ET-GH/AMBAR/AMBAR Ground Station mac build/GroundStation_autogen/EWIEGA46WW/moc_flightgraphcontroller.cpp

/****************************************************************************
** Meta object code from reading C++ file 'flightgraphcontroller.h'
**
** Created by: The Qt Meta Object Compiler version 69 (Qt 6.11.1)
**
** WARNING! All changes made in this file will be lost!
*****************************************************************************/

#include "../../../../flightgraphcontroller.h"
#include <QtCore/qmetatype.h>

#include <QtCore/qtmochelpers.h>

#include <memory>


#include <QtCore/qxptype_traits.h>
#if !defined(Q_MOC_OUTPUT_REVISION)
#error "The header file 'flightgraphcontroller.h' doesn't include <QObject>."
#elif Q_MOC_OUTPUT_REVISION != 69
#error "This file was generated using the moc from 6.11.1. It"
#error "cannot be used with the include files from this version of Qt."
#error "(The moc has changed too much.)"
#endif

#ifndef Q_CONSTINIT
#define Q_CONSTINIT
#endif

QT_WARNING_PUSH
QT_WARNING_DISABLE_DEPRECATED
QT_WARNING_DISABLE_GCC("-Wuseless-cast")
namespace {
struct qt_meta_tag_ZN21FlightGraphControllerE_t {};
} // unnamed namespace

template <> constexpr inline auto FlightGraphController::qt_create_metaobjectdata<qt_meta_tag_ZN21FlightGraphControllerE_t>()
{
    namespace QMC = QtMocConstants;
    QtMocHelpers::StringRefStorage qt_stringData {
        "FlightGraphController",
        "appendTelemetry",
        "",
        "timeMs",
        "altitudeM",
        "velocityMps",
        "accelerationMps2",
        "predictedApogeeM",
        "targetApogeeM",
        "appendEvent",
        "message",
        "clear",
        "Mode",
        "LiveCombined",
        "Altitude",
        "Velocity",
        "Acceleration"
    };

    QtMocHelpers::UintData qt_methods {
        // Slot 'appendTelemetry'
        QtMocHelpers::SlotData<void(qint64, double, double, double, double, double)>(1, 2, QMC::AccessPublic, QMetaType::Void, {{
            { QMetaType::LongLong, 3 }, { QMetaType::Double, 4 }, { QMetaType::Double, 5 }, { QMetaType::Double, 6 },
            { QMetaType::Double, 7 }, { QMetaType::Double, 8 },
        }}),
        // Slot 'appendEvent'
        QtMocHelpers::SlotData<void(qint64, const QString &)>(9, 2, QMC::AccessPublic, QMetaType::Void, {{
            { QMetaType::LongLong, 3 }, { QMetaType::QString, 10 },
        }}),
        // Slot 'clear'
        QtMocHelpers::SlotData<void()>(11, 2, QMC::AccessPublic, QMetaType::Void),
    };
    QtMocHelpers::UintData qt_properties {
    };
    QtMocHelpers::UintData qt_enums {
        // enum 'Mode'
        QtMocHelpers::EnumData<enum Mode>(12, 12, QMC::EnumIsScoped).add({
            {   13, Mode::LiveCombined },
            {   14, Mode::Altitude },
            {   15, Mode::Velocity },
            {   16, Mode::Acceleration },
        }),
    };
    return QtMocHelpers::metaObjectData<FlightGraphController, qt_meta_tag_ZN21FlightGraphControllerE_t>(QMC::MetaObjectFlag{}, qt_stringData,
            qt_methods, qt_properties, qt_enums);
}
Q_CONSTINIT const QMetaObject FlightGraphController::staticMetaObject = { {
    QMetaObject::SuperData::link<QObject::staticMetaObject>(),
    qt_staticMetaObjectStaticContent<qt_meta_tag_ZN21FlightGraphControllerE_t>.stringdata,
    qt_staticMetaObjectStaticContent<qt_meta_tag_ZN21FlightGraphControllerE_t>.data,
    qt_static_metacall,
    nullptr,
    qt_staticMetaObjectRelocatingContent<qt_meta_tag_ZN21FlightGraphControllerE_t>.metaTypes,
    nullptr
} };

void FlightGraphController::qt_static_metacall(QObject *_o, QMetaObject::Call _c, int _id, void **_a)
{
    auto *_t = static_cast<FlightGraphController *>(_o);
    if (_c == QMetaObject::InvokeMetaMethod) {
        switch (_id) {
        case 0: _t->appendTelemetry((*reinterpret_cast<std::add_pointer_t<qint64>>(_a[1])),(*reinterpret_cast<std::add_pointer_t<double>>(_a[2])),(*reinterpret_cast<std::add_pointer_t<double>>(_a[3])),(*reinterpret_cast<std::add_pointer_t<double>>(_a[4])),(*reinterpret_cast<std::add_pointer_t<double>>(_a[5])),(*reinterpret_cast<std::add_pointer_t<double>>(_a[6]))); break;
        case 1: _t->appendEvent((*reinterpret_cast<std::add_pointer_t<qint64>>(_a[1])),(*reinterpret_cast<std::add_pointer_t<QString>>(_a[2]))); break;
        case 2: _t->clear(); break;
        default: ;
        }
    }
}

const QMetaObject *FlightGraphController::metaObject() const
{
    return QObject::d_ptr->metaObject ? QObject::d_ptr->dynamicMetaObject() : &staticMetaObject;
}

void *FlightGraphController::qt_metacast(const char *_clname)
{
    if (!_clname) return nullptr;
    if (!strcmp(_clname, qt_staticMetaObjectStaticContent<qt_meta_tag_ZN21FlightGraphControllerE_t>.strings))
        return static_cast<void*>(this);
    return QObject::qt_metacast(_clname);
}

int FlightGraphController::qt_metacall(QMetaObject::Call _c, int _id, void **_a)
{
    _id = QObject::qt_metacall(_c, _id, _a);
    if (_id < 0)
        return _id;
    if (_c == QMetaObject::InvokeMetaMethod) {
        if (_id < 3)
            qt_static_metacall(this, _c, _id, _a);
        _id -= 3;
    }
    if (_c == QMetaObject::RegisterMethodArgumentMetaType) {
        if (_id < 3)
            *reinterpret_cast<QMetaType *>(_a[0]) = QMetaType();
        _id -= 3;
    }
    return _id;
}
QT_WARNING_POP
