ET-GH/AMBAR/AMBAR Ground Station mac build/GroundStation_autogen/EWIEGA46WW/moc_importdialog.cpp

/****************************************************************************
** Meta object code from reading C++ file 'importdialog.h'
**
** Created by: The Qt Meta Object Compiler version 69 (Qt 6.11.1)
**
** WARNING! All changes made in this file will be lost!
*****************************************************************************/

#include "../../../../importdialog.h"
#include <QtCore/qmetatype.h>

#include <QtCore/qtmochelpers.h>

#include <memory>


#include <QtCore/qxptype_traits.h>
#if !defined(Q_MOC_OUTPUT_REVISION)
#error "The header file 'importdialog.h' doesn't include <QObject>."
#elif Q_MOC_OUTPUT_REVISION != 69
#error "This file was generated using the moc from 6.11.1. It"
#error "cannot be used with the include files from this version of Qt."
#error "(The moc has changed too much.)"
#endif

#ifndef Q_CONSTINIT
#define Q_CONSTINIT
#endif

QT_WARNING_PUSH
QT_WARNING_DISABLE_DEPRECATED
QT_WARNING_DISABLE_GCC("-Wuseless-cast")
namespace {
struct qt_meta_tag_ZN12importDialogE_t {};
} // unnamed namespace

template <> constexpr inline auto importDialog::qt_create_metaobjectdata<qt_meta_tag_ZN12importDialogE_t>()
{
    namespace QMC = QtMocConstants;
    QtMocHelpers::StringRefStorage qt_stringData {
        "importDialog",
        "cancelRequested",
        "",
        "reject",
        "handleCancelClicked",
        "handleCloseClicked"
    };

    QtMocHelpers::UintData qt_methods {
        // Signal 'cancelRequested'
        QtMocHelpers::SignalData<void()>(1, 2, QMC::AccessPublic, QMetaType::Void),
        // Slot 'reject'
        QtMocHelpers::SlotData<void()>(3, 2, QMC::AccessPublic, QMetaType::Void),
        // Slot 'handleCancelClicked'
        QtMocHelpers::SlotData<void()>(4, 2, QMC::AccessPrivate, QMetaType::Void),
        // Slot 'handleCloseClicked'
        QtMocHelpers::SlotData<void()>(5, 2, QMC::AccessPrivate, QMetaType::Void),
    };
    QtMocHelpers::UintData qt_properties {
    };
    QtMocHelpers::UintData qt_enums {
    };
    return QtMocHelpers::metaObjectData<importDialog, qt_meta_tag_ZN12importDialogE_t>(QMC::MetaObjectFlag{}, qt_stringData,
            qt_methods, qt_properties, qt_enums);
}
Q_CONSTINIT const QMetaObject importDialog::staticMetaObject = { {
    QMetaObject::SuperData::link<QDialog::staticMetaObject>(),
    qt_staticMetaObjectStaticContent<qt_meta_tag_ZN12importDialogE_t>.stringdata,
    qt_staticMetaObjectStaticContent<qt_meta_tag_ZN12importDialogE_t>.data,
    qt_static_metacall,
    nullptr,
    qt_staticMetaObjectRelocatingContent<qt_meta_tag_ZN12importDialogE_t>.metaTypes,
    nullptr
} };

void importDialog::qt_static_metacall(QObject *_o, QMetaObject::Call _c, int _id, void **_a)
{
    auto *_t = static_cast<importDialog *>(_o);
    if (_c == QMetaObject::InvokeMetaMethod) {
        switch (_id) {
        case 0: _t->cancelRequested(); break;
        case 1: _t->reject(); break;
        case 2: _t->handleCancelClicked(); break;
        case 3: _t->handleCloseClicked(); break;
        default: ;
        }
    }
    if (_c == QMetaObject::IndexOfMethod) {
        if (QtMocHelpers::indexOfMethod<void (importDialog::*)()>(_a, &importDialog::cancelRequested, 0))
            return;
    }
}

const QMetaObject *importDialog::metaObject() const
{
    return QObject::d_ptr->metaObject ? QObject::d_ptr->dynamicMetaObject() : &staticMetaObject;
}

void *importDialog::qt_metacast(const char *_clname)
{
    if (!_clname) return nullptr;
    if (!strcmp(_clname, qt_staticMetaObjectStaticContent<qt_meta_tag_ZN12importDialogE_t>.strings))
        return static_cast<void*>(this);
    return QDialog::qt_metacast(_clname);
}

int importDialog::qt_metacall(QMetaObject::Call _c, int _id, void **_a)
{
    _id = QDialog::qt_metacall(_c, _id, _a);
    if (_id < 0)
        return _id;
    if (_c == QMetaObject::InvokeMetaMethod) {
        if (_id < 4)
            qt_static_metacall(this, _c, _id, _a);
        _id -= 4;
    }
    if (_c == QMetaObject::RegisterMethodArgumentMetaType) {
        if (_id < 4)
            *reinterpret_cast<QMetaType *>(_a[0]) = QMetaType();
        _id -= 4;
    }
    return _id;
}

// SIGNAL 0
void importDialog::cancelRequested()
{
    QMetaObject::activate(this, &staticMetaObject, 0, nullptr);
}
QT_WARNING_POP
